seiken-dev/TinyStick/Arduino/src/octave.h

#pragma once

#define FREQ_C2 65
#define FREQ_D2 73
#define FREQ_E2 82
#define FREQ_F2 87
#define FREQ_G2 98
#define FREQ_A2 110
#define FREQ_B2 123
#define FREQ_C3 131
#define FREQ_D3 147
#define FREQ_E3 165
#define FREQ_F3 175
#define FREQ_G3 196
#define FREQ_A3 220
#define FREQ_B3 247
#define FREQ_C4 262
#define FREQ_D4 294
#define FREQ_E4 330
#define FREQ_F4 349
#define FREQ_G4 392
#define FREQ_A4 440
#define FREQ_B4 494
#define FREQ_C5 523
#define FREQ_D5 587
#define FREQ_E5 659
#define FREQ_F5 698
#define FREQ_G5 784
#define FREQ_A5 880
#define FREQ_B5 988
#define FREQ_C6 1046
#define FREQ_D6 1175
#define FREQ_E6 1318
#define FREQ_F6 1397
#define FREQ_G6 1568
#define FREQ_A6 1760
#define FREQ_B6 1865
#define FREQ_C7 2093
#define FREQ_D7 2349
#define FREQ_E7 2637
#define FREQ_F7 2794
#define FREQ_G7 3136
#define FREQ_A7 3520
#define FREQ_B7 3951
#define FREQ_C8 4186
